Nischay2312/sharingan-eyes/preview_fx.png

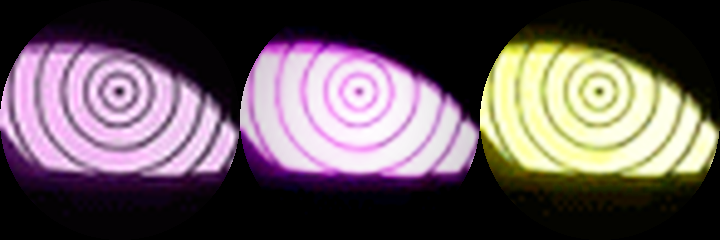
preview_fx.png
