Nischay2312/sharingan-eyes/tools/_test_loop.gif

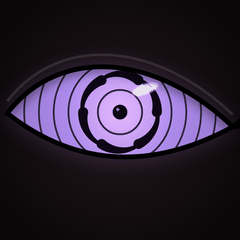
tools/_test_loop.gif
