Nischay2312/sharingan-eyes/tools/_test_loopframes.png

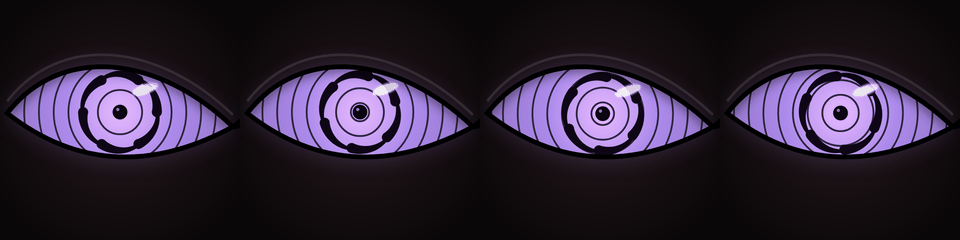
tools/_test_loopframes.png
