Nischay2312/sharingan-eyes/tools/_test_mangekyou.png

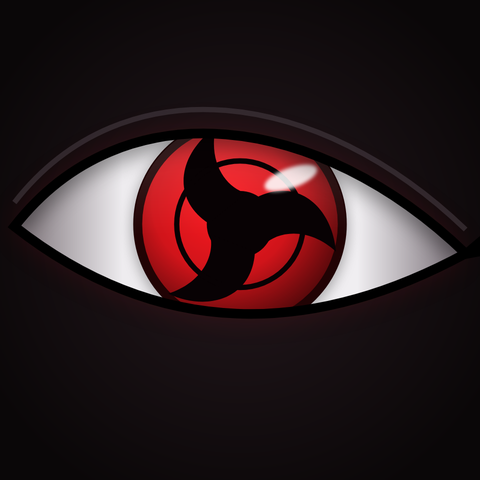
tools/_test_mangekyou.png
