Nischay2312/sharingan-eyes/tools/_test_rinnegan.png

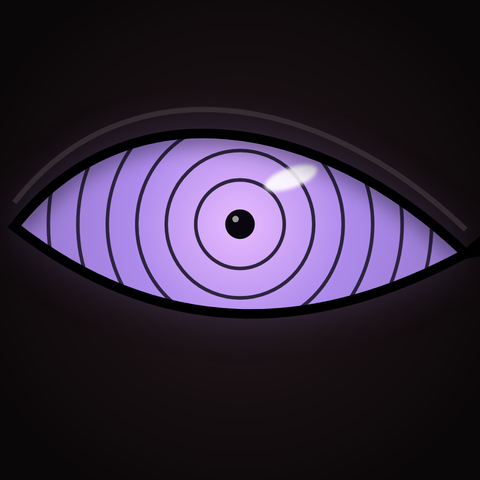
tools/_test_rinnegan.png
