Nischay2312/sharingan-eyes/tools/_test_tomoe3.png

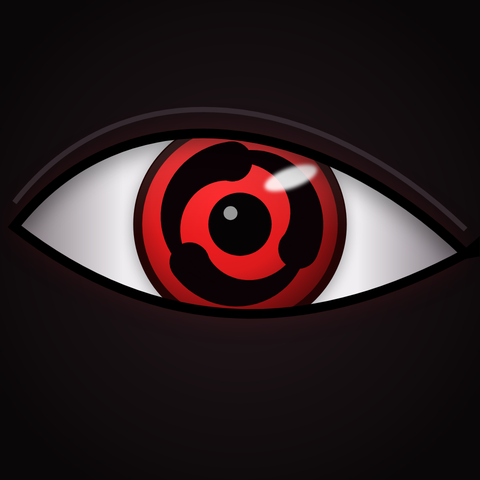
tools/_test_tomoe3.png
