Nischay2312/sharingan-eyes/tools/_test_tomoerin.png

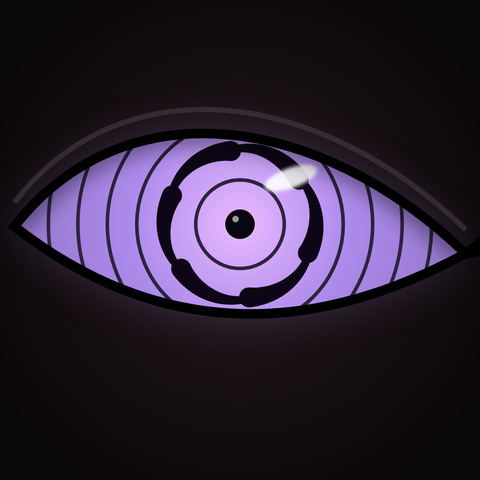
tools/_test_tomoerin.png
